faliqadlan/pertacoustic-3d-design/.agents/context/biweekly-5/project.md

# Biweekly 5 Working Context

**Status:** Preliminary package executed; screening status is PASS
**Reporting deadline:** 30 July 2026
**Scope:** AI context for the Biweekly 5 milestone

## Relationship to Repository Context

- `.agents/context/project.md` describes the verified repository-wide state.
- This file narrows that context to Biweekly 5.
- Earlier PDFs in `biweekly-2/` and `biweekly-4/` are continuity and formatting references, not factual authority for the new design.

## Intended Milestone

Prepare an evidence-based 3D casing concept that can connect to the HTI-02-DHPC/D mechanical interface shown in `HTI-02-DHPC_D MECH OUTLINE_.pdf`, then document the actual progress in a separate Indonesian Markdown report for transfer to Google Docs.

## Current State

- The supplier mechanical outline is present and is the controlling local reference for the interface.
- The previous generated hydrophone envelope, threaded adapter, and assembly code were removed because their dimensions contradicted the drawing and their solids overlapped.
- `results/biweekly-5/` contains the Indonesian Markdown report, final presentation/analysis STEP files, figures, tabular results, run inputs, and solver summaries.
- The reference design uses a nominal 7/16-20 UNF-2A male adapter, a separate pressure-seal area, three provisional conductors, and axial electronics envelopes.
- A 41 mm clear internal diameter is required by the provisional PCM1808 envelope and 1.5 mm clearance. The 43 mm and 50 mm OD candidates fail the resulting fit screen.
- The revised thermal-priority concept is 200 mm OD and 425 mm long: 35 mm Inconel 718 barrel, 50 mm endcaps, 42.5 mm sealed radial aerogel, 2 mm PEEK, 41 mm clear ID, and 50/71 mm front/rear axial aerogel buffers.
- The closed 3D one-hour/1 W thermal model includes both endcaps and axial buffers. The fine maximum electronics-boundary temperature is 62.8849 C and thermal medium-to-fine change is 1.1799%, so the stated 70 C screening limit passes. Boards are not modeled as solids, so these remain cavity-boundary rather than chip-junction temperatures.
- The simplified structural scope uses Lamé/yield and long-cylinder buckling calculations plus three static pressure meshes at 10,000 psi. Fine static stress is 212.51 MPa, displacement is 0.785 mm, analytical yield FoS is 4.84, and analytical buckling factor is 18.04. This is preliminary screening, not eigenvalue-buckling convergence or pressure-vessel certification.
- The detailed CAD now includes the longer housing, separate 50 mm endcaps, relocated electronics, and front/rear axial aerogel buffers. Seal grooves, contacts, thread tolerances, and certified pressure retention remain conceptual.
- Gmsh fragment-to-material mapping and solver success detection now fail closed; stale FRD files and CalculiX fatal text cannot be reported as successful reruns.
- The thermal workflow previously divided conductivity by 1,000. That unit error was fixed; the old near-25 C result is invalid and must not be cited.
- The user excluded vacuum insulation and added thermal-mass blocks because the tool must be made with conventional CNC and assembly capability at the UGM Geophysics Laboratory.

## Execution Guardrails

- Treat the generated report as preliminary engineering, not manufacturing approval or certification.
- Do not describe removed Antigravity outputs as progress or evidence.
- Distinguish drawing dimensions, user requirements, derived calculations, modeling assumptions, and verified CAD results.
- Do not claim pressure integrity, sealing performance, structural strength, manufacturability, or certification without corresponding evidence.
- Preserve the prior reports and supplier drawing unchanged.
- Prefer a concise milestone report unless the user requests the full long-form structure used previously.

## Decisions Needed Before Manufacturing-Grade Design

1. Obtain the supplier-controlled HTI drawing, pinout, preamplifier mode, cable, and endcap configuration.
2. Measure the purchased boards and confirm maximum tool OD/length.
3. Select exact Inconel heat treatment, aerogel/PEEK grades, seal system, and well-fluid/sour-service requirements.
4. Physically validate the thermal stack and pressure hardware before treating preliminary screening as a manufacturing design.

## Package Acceptance Criteria

- Future agents load this file only when working on Biweekly 5.
- Reproduce results with `.\.venv\Scripts\python.exe -m cosmo.biweekly5` before changing reported values.
- Preserve the explicit distinction between reference dimensions, assumptions, calculations, and solver results.
