faliqadlan/pertacoustic-3d-design/results/compact-casing/figures/compact_cad_assembly.png

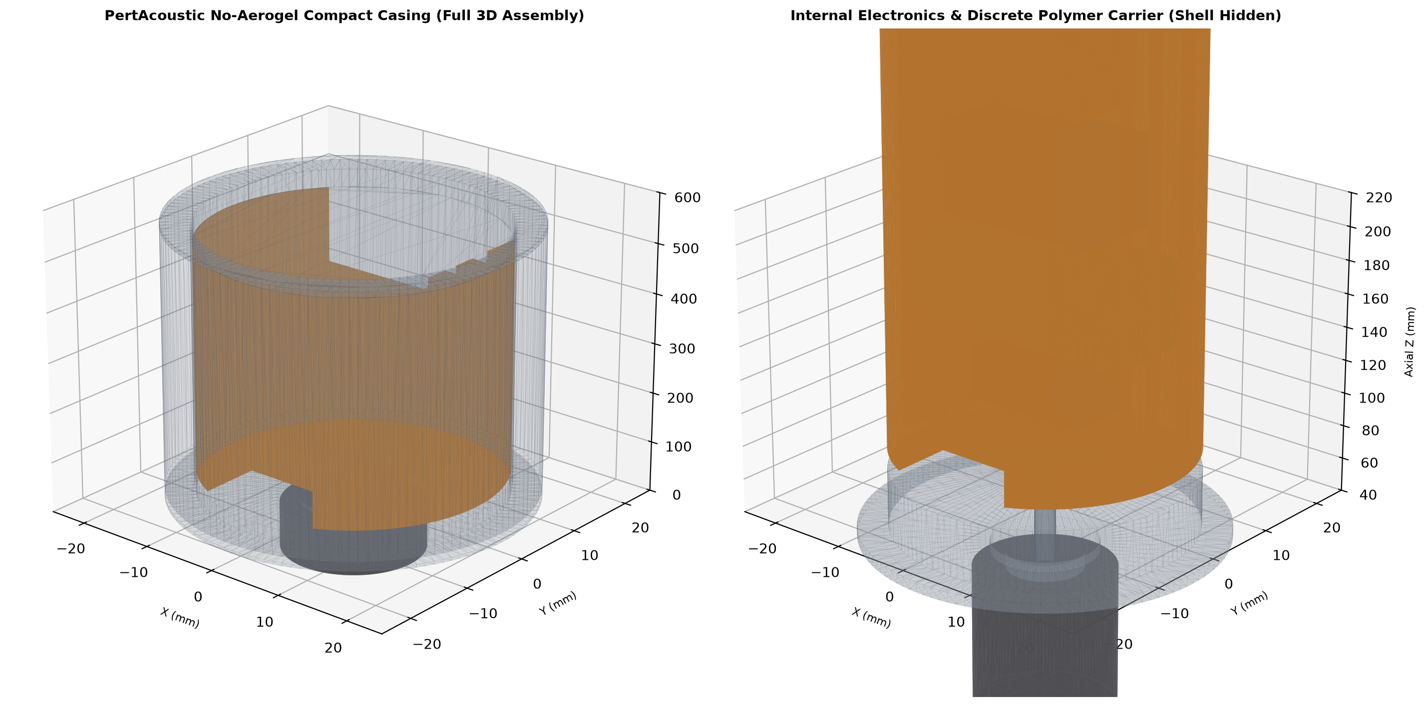
results/compact-casing/figures/compact_cad_assembly.png
