faliqadlan/pertacoustic-3d-design/results/compact-casing/figures/compact_longitudinal_section.png

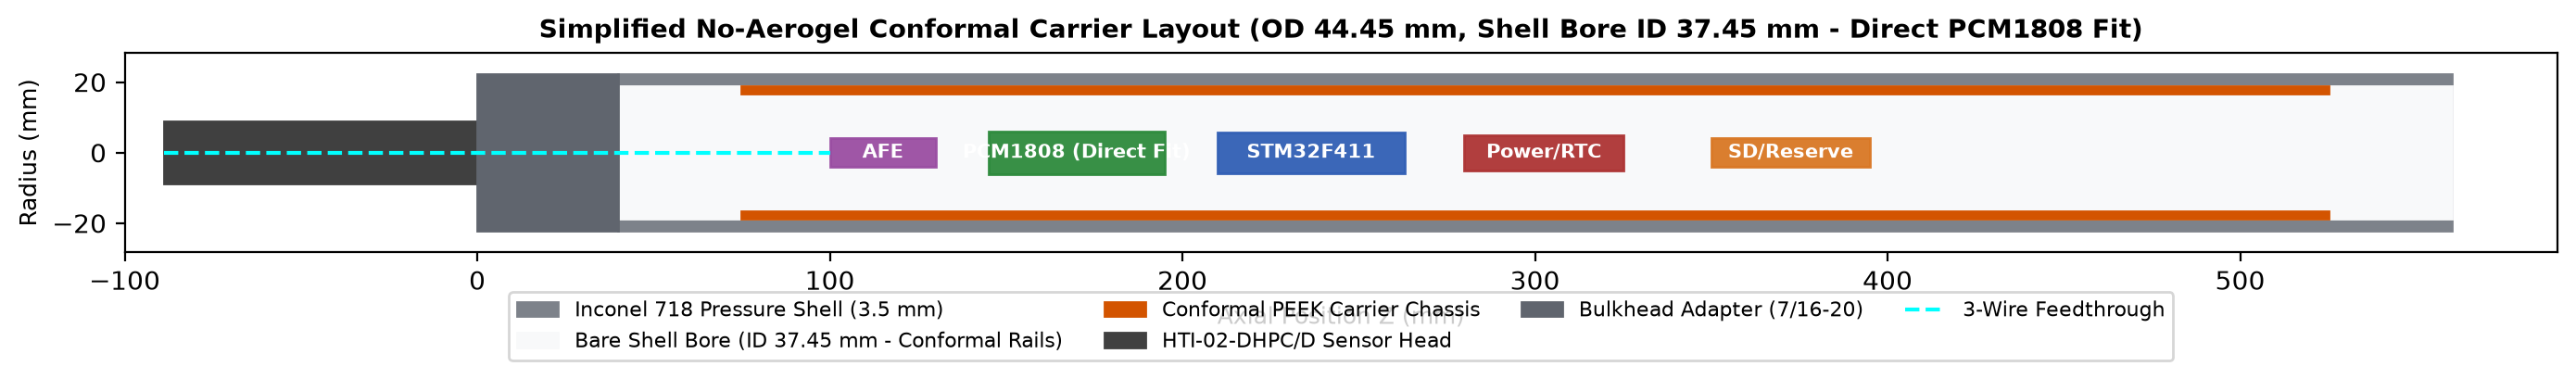
results/compact-casing/figures/compact_longitudinal_section.png
