faliqadlan/pertacoustic-3d-design/results/compact-casing/figures/compact_thermal_trade_study.png

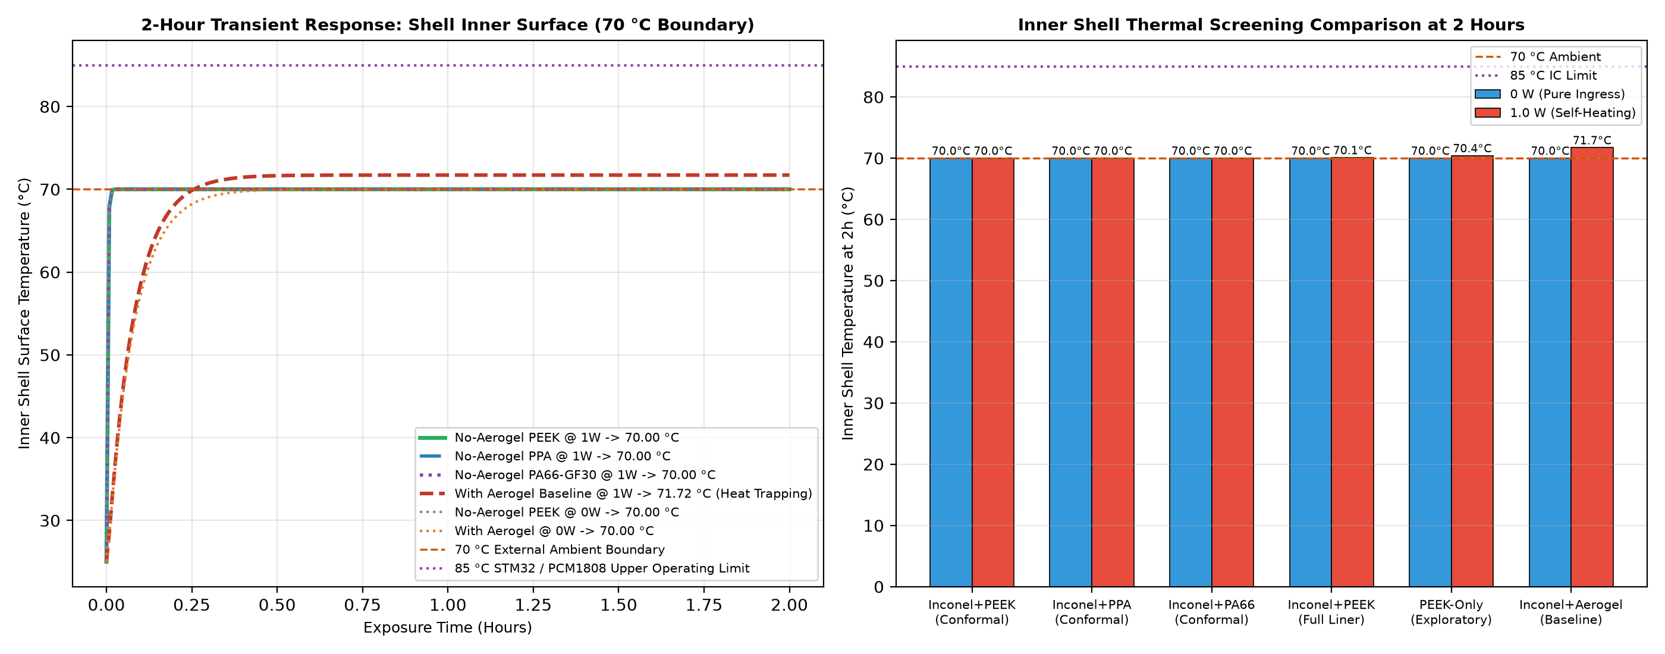
results/compact-casing/figures/compact_thermal_trade_study.png
