faliqadlan/pertacoustic-3d-design/results/compact-casing/figures/compact_transverse_pcm1808_section.png

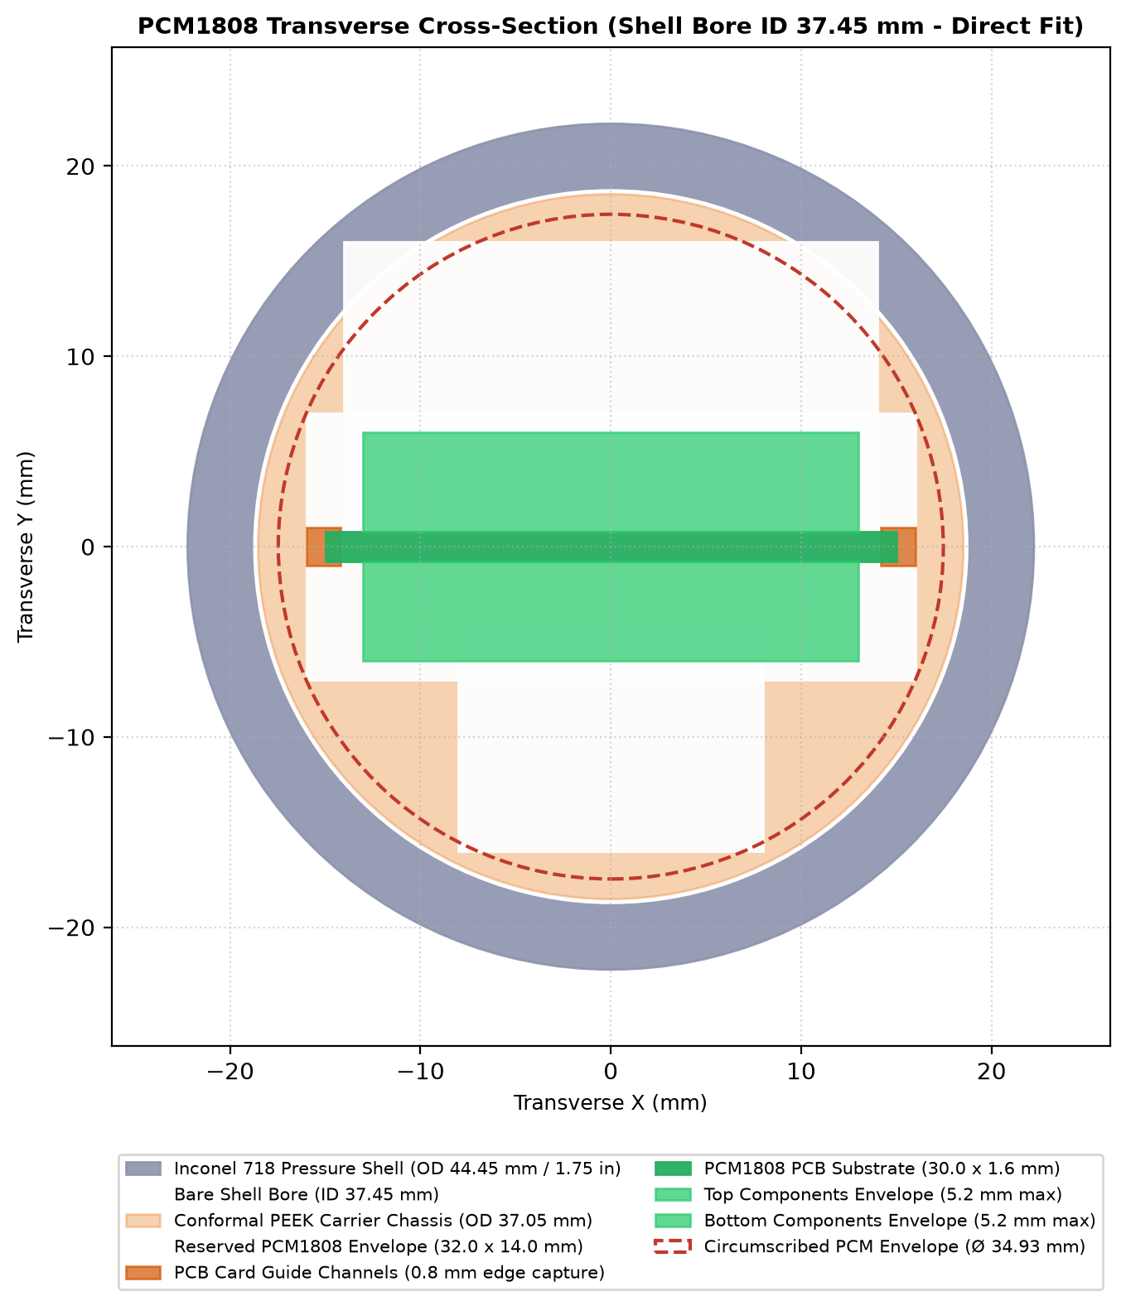
results/compact-casing/figures/compact_transverse_pcm1808_section.png
